smartstetho-team/SmartStethoscope/mechanical/V3/Mic.SLDPRT

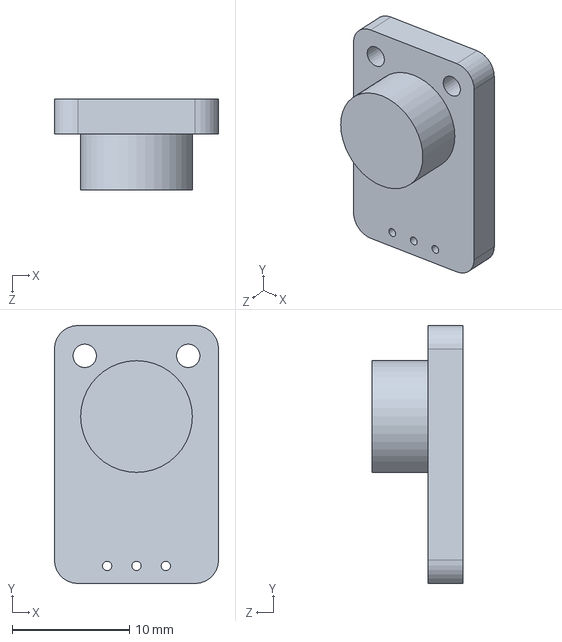
[picture p18: CAD file, 2025-11-20]
mechanical/V3/Mic.SLDPRT
14.0 x 22.0 x 7.76 mm
