smartstetho-team/SmartStethoscope/mechanical/V3/adapter.SLDPRT

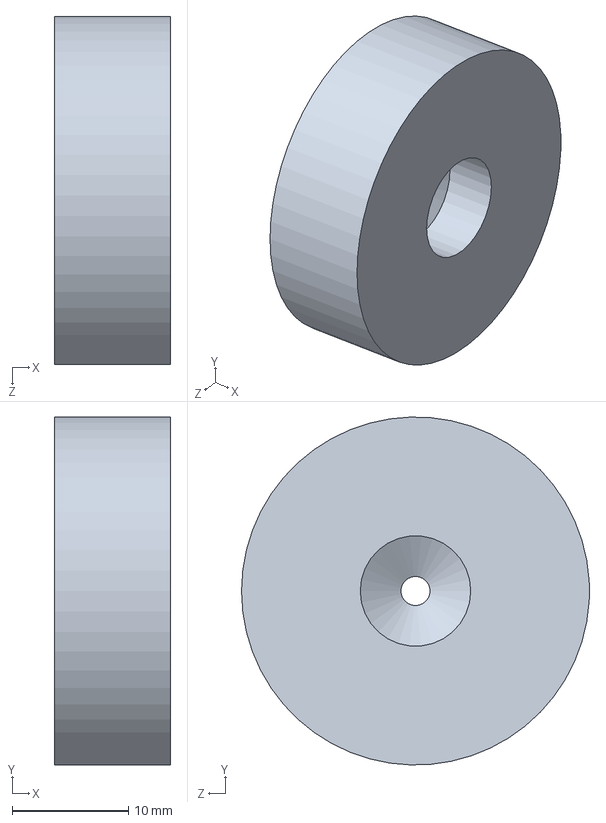
[picture p19: CAD file, 2025-11-20]
mechanical/V3/adapter.SLDPRT
10.0 x 30.0 x 30.0 mm
