smartstetho-team/SmartStethoscope/mechanical/V3/Button.SLDPRT

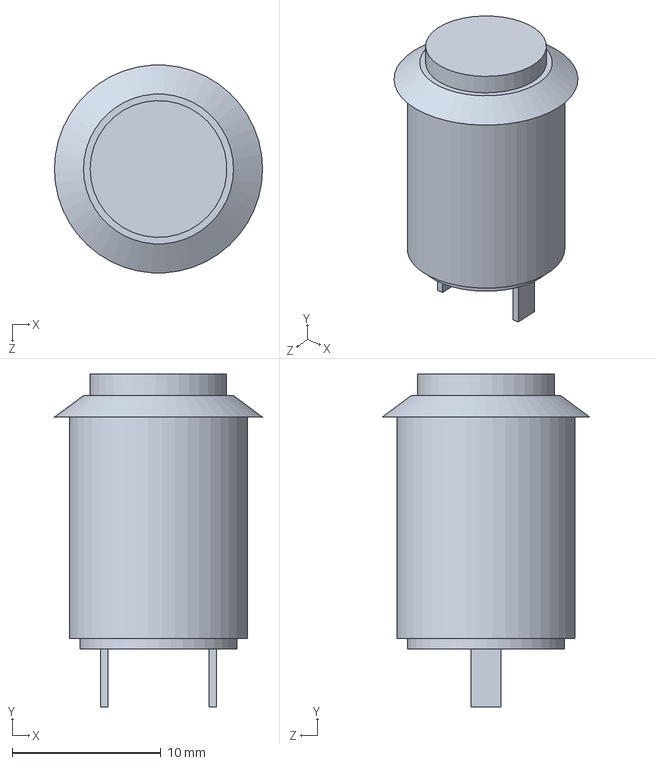
[picture p20: CAD file, 2025-11-20]
mechanical/V3/Button.SLDPRT
14.0 x 22.4 x 14.0 mm
