smartstetho-team/SmartStethoscope/mechanical/V3/BodyPlastic.SLDPRT

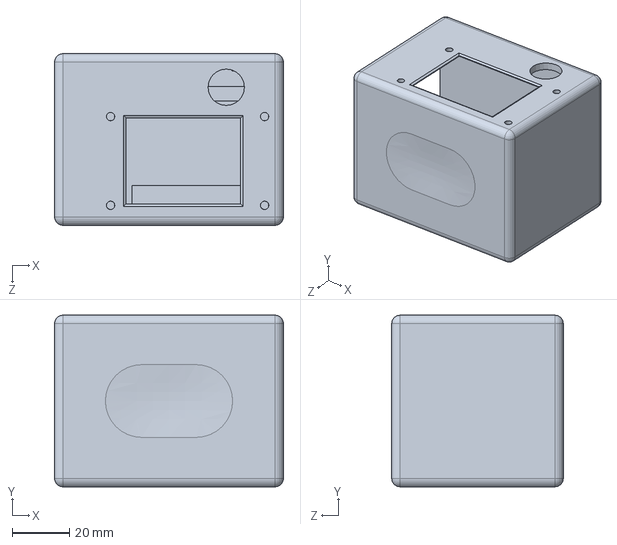
[picture p21: CAD file, 2025-11-20]
mechanical/V3/BodyPlastic.SLDPRT
80.0 x 60.0 x 60.0 mm
