smartstetho-team/SmartStethoscope/mechanical/V3/battery.SLDPRT

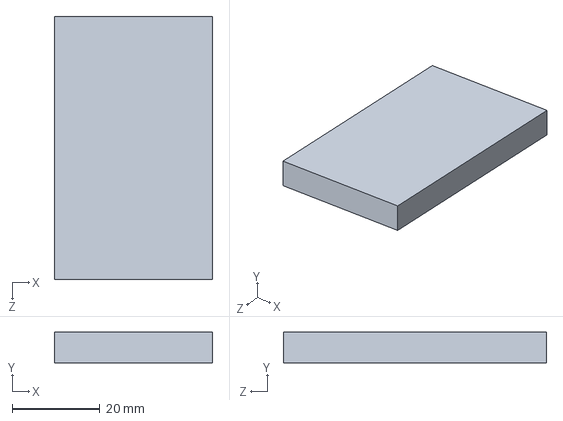
[picture p22: CAD file, 2025-11-20]
mechanical/V3/battery.SLDPRT
36.0 x 7.00 x 60.0 mm
