smartstetho-team/SmartStethoscope/mechanical/V3/TopLevel.SLDASM

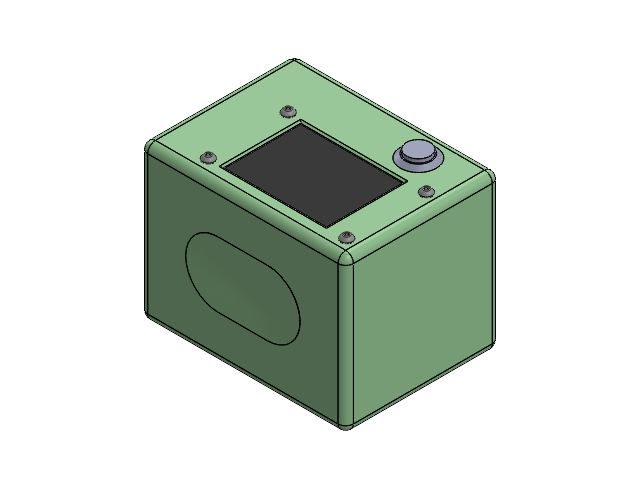
[picture p23: CAD file, 2025-11-20]
mechanical/V3/TopLevel.SLDASM
BodyPlastic
Button
Screen
battery
esp2
92095A460_Button Head Hex Drive Screw x 4
