smartstetho-team/SmartStethoscope/testing/ml/graphs/metric_comparision.png

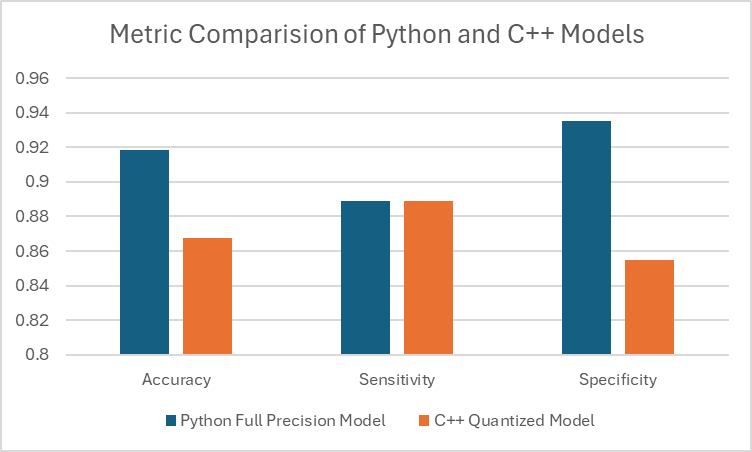
testing/ml/graphs/metric_comparision.png
