smartstetho-team/SmartStethoscope/testing/ml/graphs/model_output_diff.png

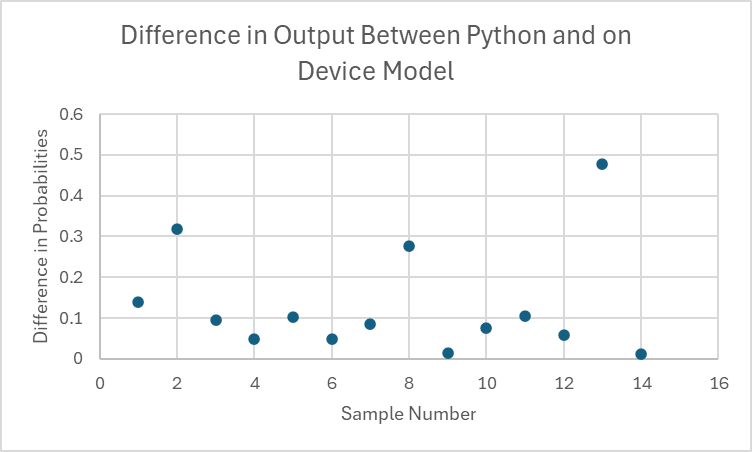
testing/ml/graphs/model_output_diff.png
