smartstetho-team/SmartStethoscope/firmware/main/src/drivers/lcd_display.cpp

/*
 Reference Documentation:
- https://docs.espressif.com/projects/esp-idf/en/stable/esp32/api-reference/peripherals/lcd/index.html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
- https://docs.lvgl.io/master/examples.html
- https://github.com/ryanfkeller/hello-lvgl-esp-idf
*/

#include "drivers/lcd_display.h"

#include "driver/gpio.h"
#include "driver/spi_master.h"
#include "esp_log.h"
#include "lvgl.h"
#include "esp_timer.h"

static const char *LCD_DISPLAY_DRIVER_TAG = "LCD_DISPLAY_DRIVER";

static void lvgl_flush_cb(lv_display_t *disp, const lv_area_t *area, uint8_t *px_map)
{
    // Get the LCD handle and pixel offset
    esp_lcd_panel_handle_t panel_handle = (esp_lcd_panel_handle_t)lv_display_get_user_data(disp);

    int offsetx1 = area->x1;
    int offsetx2 = area->x2; 
    int offsety1 = area->y1;
    int offsety2 = area->y2;

    // because SPI LCD is big-endian, we need to swap the RGB bytes order
    lv_draw_sw_rgb565_swap(px_map, (offsetx2 + 1 - offsetx1) * (offsety2 + 1 - offsety1));

    // copy a buffer's content to a specific area of the display
    esp_lcd_panel_draw_bitmap(panel_handle, offsetx1, offsety1, offsetx2 + 1, offsety2 + 1, px_map); // is what draws everything
}

static void increase_lvgl_tick(void *arg)
{
    /* Tell LVGL how many milliseconds has elapsed */
    lv_tick_inc(LVGL_TICK_PERIOD_MS);
}

static bool notify_lvgl_flush_ready(
    esp_lcd_panel_io_handle_t panel_io,
    esp_lcd_panel_io_event_data_t *edata,
    void *user_ctx)
{
    lv_display_t *disp = (lv_display_t *)user_ctx;
    lv_display_flush_ready(disp);
    return false;
}

void configure_lcd_display(LCD_Display_Params * lcd_params)
{
    // Turn on LCD backlight
    gpio_config_t bk_gpio_config = 
    {
        .pin_bit_mask = 1 << BK_LIGHT_GPIO_PIN,
        .mode = GPIO_MODE_OUTPUT,
    };
    ESP_ERROR_CHECK(gpio_config(&bk_gpio_config));
    ESP_ERROR_CHECK(gpio_set_level(BK_LIGHT_GPIO_PIN, 1));

    // Set up SPI Bus
    spi_bus_config_t bus = {0};
    bus.mosi_io_num = MOSI_GPIO_PIN;
    bus.miso_io_num = MISO_GPIO_PIN;
    bus.sclk_io_num = SCLK_GPIO_PIN;
    bus.quadwp_io_num = -1;
    bus.quadhd_io_num = -1;
    bus.max_transfer_sz = LCD_DISPLAY_HEIGHT_PXLS * LCD_DISPLAY_WIDTH_PXLS * sizeof(uint16_t);
    ESP_ERROR_CHECK(spi_bus_initialize(LCD_HOST, &bus, SPI_DMA_CH_AUTO));

    // Connect LCD panel to the SPI bus
    lcd_params->io_handle = NULL;
    lcd_params->io_config = 
    {
        .cs_gpio_num = LCD_CS_GPIO_PIN,
        .dc_gpio_num = LCD_DC_GPIO_PIN,
        .spi_mode = 0,
        .pclk_hz = 10000000, // 10 MHz SPI Clock Frequency 
        .trans_queue_depth = 10,
        .on_color_trans_done = NULL,
        .user_ctx = NULL,
        .lcd_cmd_bits = 8,
        .lcd_param_bits = 8,
        .flags = {0} 
    };
    ESP_ERROR_CHECK(esp_lcd_new_panel_io_spi((esp_lcd_spi_bus_handle_t)LCD_HOST, 
                    &lcd_params->io_config, &lcd_params->io_handle));

    // Install ST7789 Driver
    lcd_params->panel_handle = NULL; 
    lcd_params->panel_config = 
    {
        .reset_gpio_num = LCD_RESET_GPIO_PIN,
        .rgb_ele_order = LCD_RGB_ELEMENT_ORDER_RGB,
        .data_endian = LCD_RGB_DATA_ENDIAN_BIG,
        .bits_per_pixel = 16,
        .flags = { .reset_active_high = 0 },
        .vendor_config = NULL
    };
    ESP_ERROR_CHECK(esp_lcd_new_panel_st7789(lcd_params->io_handle, &lcd_params->panel_config, 
                    &lcd_params->panel_handle));

    // Initialize and Configure LCD Display
    ESP_ERROR_CHECK(esp_lcd_panel_reset(lcd_params->panel_handle));
    vTaskDelay(pdMS_TO_TICKS(150));
    ESP_ERROR_CHECK(esp_lcd_panel_init(lcd_params->panel_handle));
    vTaskDelay(pdMS_TO_TICKS(150));

    ESP_ERROR_CHECK(esp_lcd_panel_set_gap(lcd_params->panel_handle, 0, 0));
    ESP_ERROR_CHECK(esp_lcd_panel_swap_xy(lcd_params->panel_handle, true));
    ESP_ERROR_CHECK(esp_lcd_panel_mirror(lcd_params->panel_handle, true, false));

    ESP_ERROR_CHECK(esp_lcd_panel_invert_color(lcd_params->panel_handle, true));
    ESP_ERROR_CHECK(esp_lcd_panel_disp_on_off(lcd_params->panel_handle, true)); // Display turned off by default

    ESP_LOGI(LCD_DISPLAY_DRIVER_TAG, "LCD Display Setup Complete.");
}

void configure_lcd_lvgl(LCD_Display_Params * lcd_params)
{
    lv_init();

    lv_display_t *display = lv_display_create(LCD_DISPLAY_HEIGHT_PXLS, LCD_DISPLAY_WIDTH_PXLS);

    size_t draw_buffer_sz = LCD_DISPLAY_HEIGHT_PXLS * LVGL_DRAW_BUF_LINES * sizeof(lv_color16_t);

    lcd_params->display_buffer1 = spi_bus_dma_memory_alloc(LCD_HOST, draw_buffer_sz, 0);
    lcd_params->display_buffer2 = spi_bus_dma_memory_alloc(LCD_HOST, draw_buffer_sz, 0);

    if ((lcd_params->display_buffer1 == nullptr) || (lcd_params->display_buffer2 == nullptr))
    {
        ESP_LOGE(LCD_DISPLAY_DRIVER_TAG, "SPI DMA Buffers Allocation Failed!");
    }

    lv_display_set_buffers(display, lcd_params->display_buffer1, lcd_params->display_buffer2, 
                           draw_buffer_sz, LV_DISPLAY_RENDER_MODE_PARTIAL);

    lv_display_set_user_data(display, lcd_params->panel_handle);

    lv_display_set_color_format(display, LV_COLOR_FORMAT_RGB565); // R - 5 bits, G - 6 bits, B - 5 bits

    lv_display_set_flush_cb(display, lvgl_flush_cb);

    const esp_timer_create_args_t lvgl_tick_timer_args = 
    {
        .callback = &increase_lvgl_tick,
        .name = "lvgl_tick"
    };

    esp_timer_handle_t lvgl_tick_timer = NULL;

    ESP_ERROR_CHECK(esp_timer_create(&lvgl_tick_timer_args, &lvgl_tick_timer));
    ESP_ERROR_CHECK(esp_timer_start_periodic(lvgl_tick_timer, LVGL_TICK_PERIOD_MS * 1000));

    const esp_lcd_panel_io_callbacks_t cbs = 
    {
        .on_color_trans_done = notify_lvgl_flush_ready,
    };

    ESP_ERROR_CHECK(esp_lcd_panel_io_register_event_callbacks(lcd_params->io_handle, &cbs, display));
}
