smartstetho-team/SmartStethoscope/firmware/main/scripts/record_over_serial.py

import struct
import sys as sys
import time
import wave

import numpy as np
import serial

PORT = "COM5"  # adjust if different
# PORT = "/dev/cu.usbmodem101" # macOS
BAUD = 921600
SAMPLE_RATE = 8000
RECORD_SECONDS = 10
NUM_SAMPLES = SAMPLE_RATE * RECORD_SECONDS

OUTPUT_WAV = "../recordings/stethoscope_raw_audio.wav"

print("Opening serial port...")
ser = serial.Serial()
ser.port = PORT
ser.baudrate = BAUD
ser.timeout = 2
ser.dsrdtr = False
ser.rtscts = False
ser.dtr = False
ser.rts = False
ser.open()

# Give board time + flush any old text
time.sleep(2)
ser.reset_input_buffer()

cmd = sys.argv[1]
print(f"Sending '{cmd}' to start recording...")
ser.write(cmd.encode())

print("Reading samples from ESP32...")
needed_bytes = NUM_SAMPLES * 4
buf = bytearray()

while len(buf) < needed_bytes:
    chunk = ser.read(needed_bytes - len(buf))
    if not chunk:
        # no more data within timeout
        break
    buf.extend(chunk)

ser.close()

print(f"Collected {len(buf)//4} samples (expected {NUM_SAMPLES}).")

if len(buf) < 2:
    print("No data, nothing to save.")
    raise SystemExit

# Convert bytes -> numpy array
samples = []
for i in range(0, len(buf), 4):
    if i + 2 > len(buf): 
        break
    (raw_val,) = struct.unpack('>H', buf[i:i+2])  # 0..4095-ish
    value = raw_val & 0x0FFF
    samples.append(value)

samples = np.array(samples, dtype=np.float32)

# Map ADC 0-4095 -> -1.0 .. 1.0
samples = (samples / 4095.0) * 2.0 - 1.0

samples_pcm = (samples * 32767).astype(np.int16)

with wave.open(OUTPUT_WAV, "w") as wf:
    wf.setnchannels(1)
    wf.setsampwidth(2)      # 16-bit
    wf.setframerate(SAMPLE_RATE)
    wf.writeframes(samples_pcm.tobytes())

print(f"Saved RAW {OUTPUT_WAV}")
